fuseoppl/Amiga_CD32_CD_ROM_sniffer/OLedI2C.h

/*
	OLedI2C.h
	OLED 1602 Library for the I2C
	OLED display from WIDE.HK
	Also my first attempt at a Library
	Phil Grant Sept 2013
	www.gadjet.co.uk
	Scrolling contributed by Nathan Chantrell http://nathan.chantrell.net/
	Updated 06/11/2013 to include the cursPos data within the sendString function.
*/
#ifndef OLedI2C_h
#define OLedI2C_h	
#include "Arduino.h"
#include "Wire.h"

class OLedI2C {
public:
		OLedI2C();
		~OLedI2C();
		void init();
		void sendCommand(unsigned char command); // unsigned char
		void print(const char *String); // *String
		void sendString(const char *String, uint8_t col, uint8_t row); // *String, column, row
		void sendFloat(float digit, uint8_t dec, uint8_t nad, uint8_t col, uint8_t row); // float, digits, decimal, column, row
		void sendData(unsigned char data);
		void clearLcd();
		void setCursor(uint8_t, uint8_t); // column, row
		void scrollString(char* message, byte row, unsigned int time); //written by Nathan Chantrell http://nathan.chantrell.net/
		void lcdOff();
		void lcdOn();
		void setContrast(unsigned char contrast); // contrast should be the hex value between 0x00 and 0xFF
};
#endif
